UTS-500-Series/Compressor/kicad/connector.kicad_sch

## KiCad design kicad/connector.kicad_sch (2026-10-02)

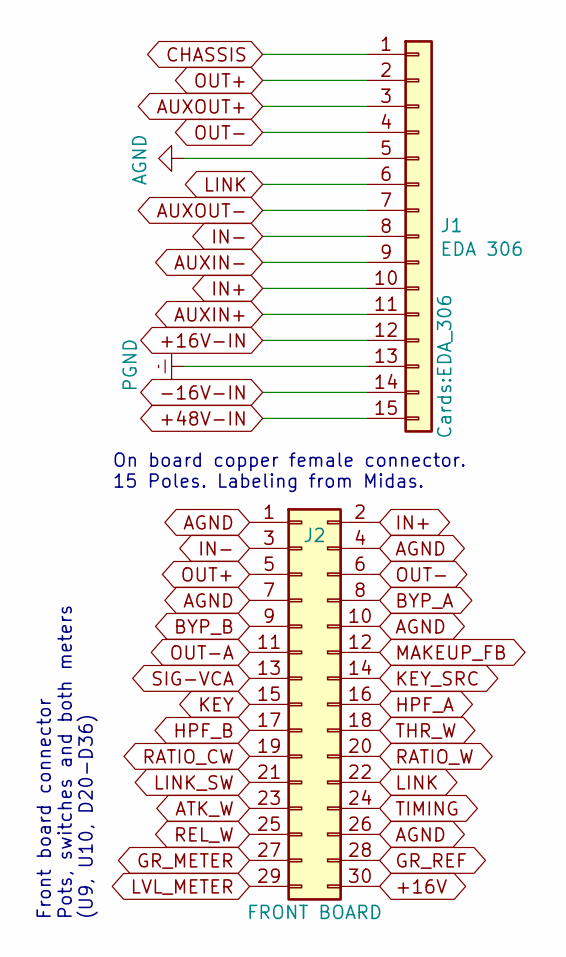
[picture p19: schematic connector.kicad_sch]

Parts:
J1: EDA 306; EDA_306
J2: FRONT BOARD; IDC-Header_2x15_P2.54mm_Vertical

Connections:
+16V: J2.30
+16V-IN: J1.12
+48V-IN: J1.15
-16V-IN: J1.14
AGND: J1.5, J2.1, J2.4, J2.7, J2.10, J2.26
ATK_W: J2.23
AUXIN+: J1.11
AUXIN-: J1.9
AUXOUT+: J1.3
AUXOUT-: J1.7
BYP_A: J2.8
BYP_B: J2.9
CHASSIS: J1.1
GR_METER: J2.27
GR_REF: J2.28
HPF_A: J2.16
HPF_B: J2.17
IN+: J1.10, J2.2
IN-: J1.8, J2.3
KEY: J2.15
KEY_SRC: J2.14
LINK: J1.6, J2.22
LINK_SW: J2.21
LVL_METER: J2.29
MAKEUP_FB: J2.12
OUT+: J1.2, J2.5
OUT-: J1.4, J2.6
OUT-A: J2.11
PGND: J1.13
RATIO_CW: J2.19
RATIO_W: J2.20
REL_W: J2.25
SIG-VCA: J2.13
THR_W: J2.18
TIMING: J2.24

Notes on the sheet:
Front board connector Pots, switches and both meters (U9, U10, D20-D36)
On board copper female connector. 15 Poles. Labeling from Midas.
