UTS-500-Series/Compressor/kicad/input.kicad_sch

## KiCad design kicad/input.kicad_sch (2026-10-02)

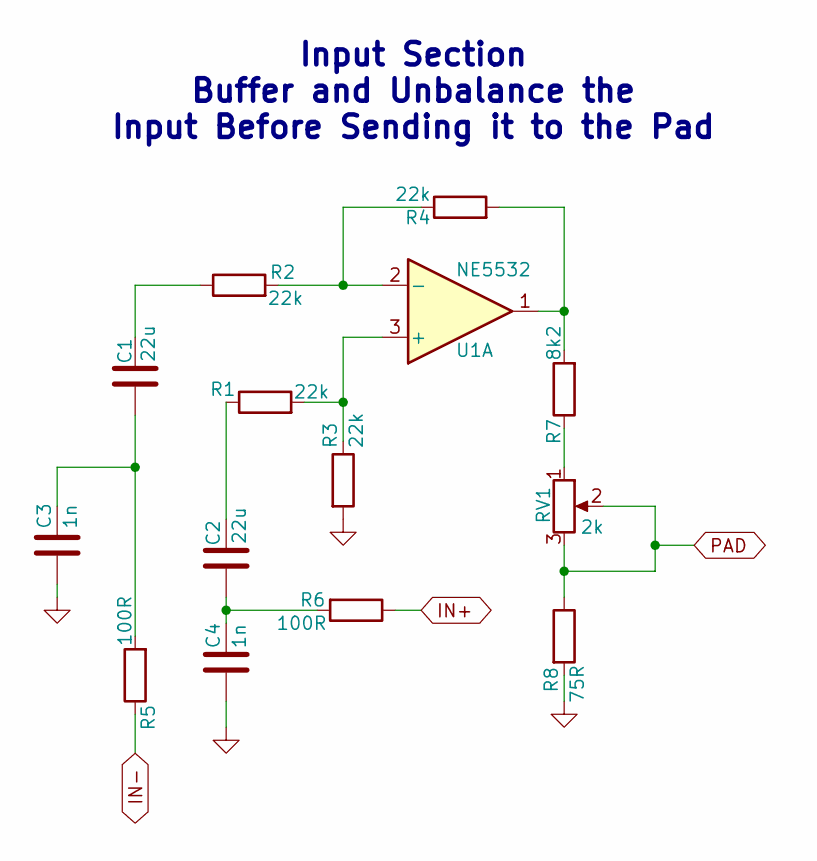
[picture p20: schematic input.kicad_sch]

Parts:
C1, C2: 22u; CP_Radial_D6.3mm_P2.50mm
C3, C4: 1n; C_Disc_D5.0mm_W2.5mm_P5.00mm
R1, R2, R3, R4: 22k; R_Axial_DIN0207_L6.3mm_D2.5mm_P10.16mm_Horizontal
R5, R6: 100R; R_Axial_DIN0207_L6.3mm_D2.5mm_P10.16mm_Horizontal
R7: 8k2; R_Axial_DIN0207_L6.3mm_D2.5mm_P10.16mm_Horizontal
R8: 75R; R_Axial_DIN0207_L6.3mm_D2.5mm_P10.16mm_Horizontal
RV1: 2k; Potentiometer_Bourns_3296W_Vertical
U1: NE5532; DIP-8_W7.62mm_Socket

Connections:
AGND: C3.2, C4.2, R3.2, R8.2
IN+: R6.1
IN-: R5.1
unnamed: C1.1, C3.1, R5.2
unnamed: C1.2, R2.1
unnamed: C2.1, C4.1, R6.2
unnamed: C2.2, R1.1
unnamed: R1.2, R3.1, U1.3 (+)
unnamed: R2.2, R4.1, U1.2 (-)
unnamed: R4.2, R7.2, U1.1
unnamed: R7.1, RV1.1
PAD: R8.1, RV1.2, RV1.3

Notes on the sheet:
Input Section Buffer and Unbalance the Input Before Sending it to the Pad
