UTS-500-Series/Compressor/kicad/meters.kicad_sch

## KiCad design kicad/meters.kicad_sch (2026-10-03)

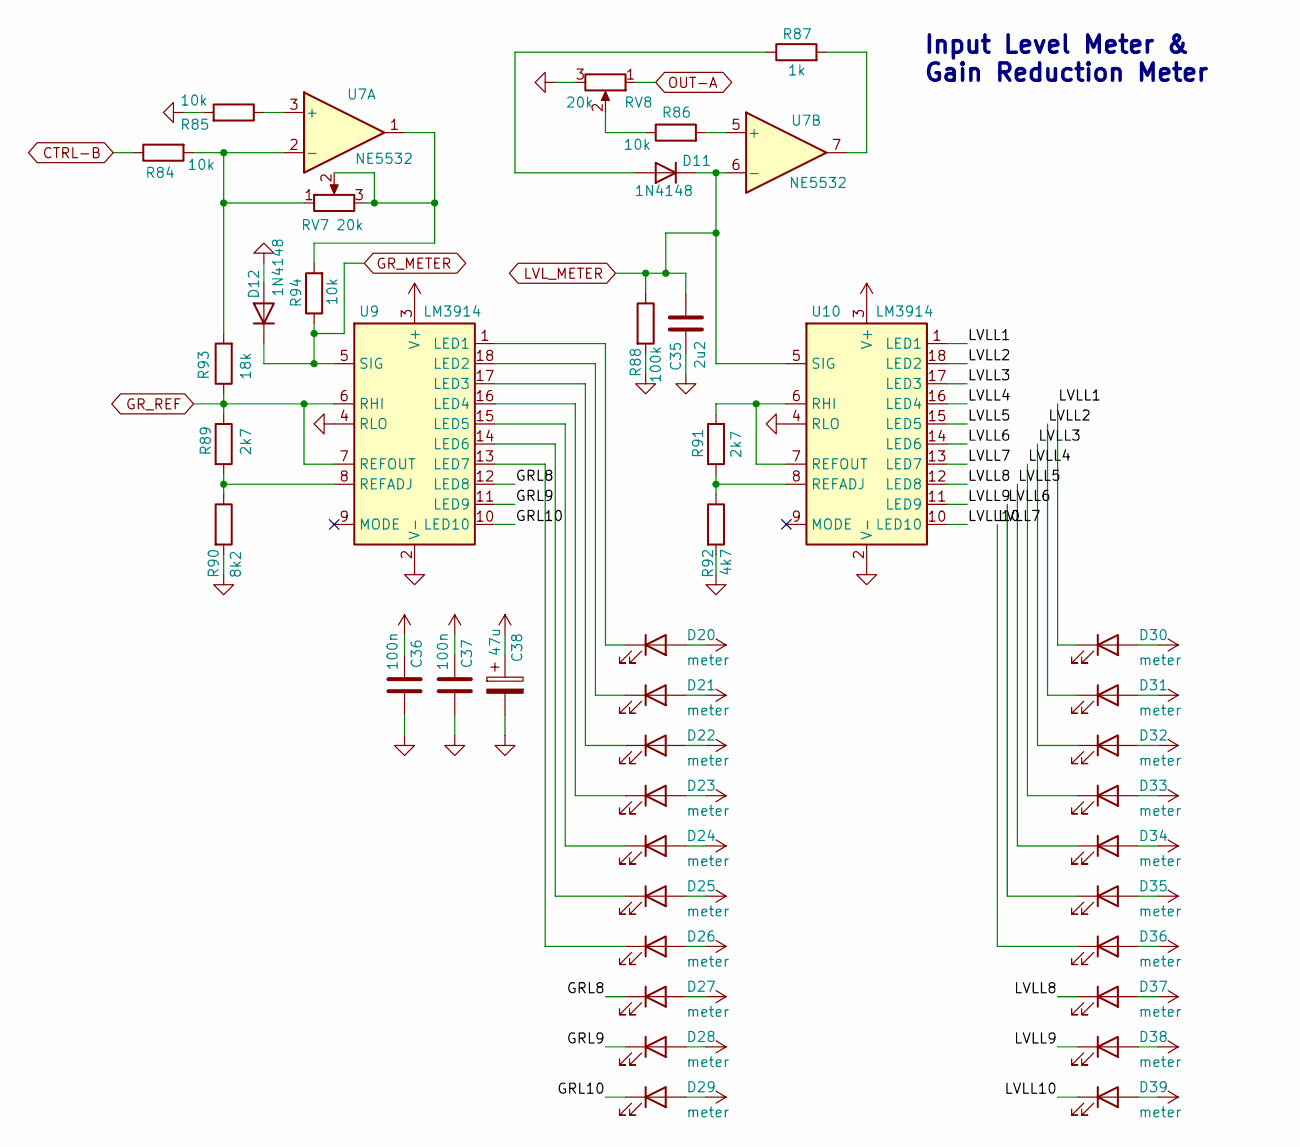
[picture p21: schematic meters.kicad_sch]

Parts:
C35: 2u2; C_Rect_L7.2mm_W7.2mm_P5.00mm_FKS2_FKP2_MKS2_MKP2
C36, C37: 100n; C_Disc_D5.0mm_W2.5mm_P5.00mm
C38: 47u; CP_Radial_D6.3mm_P2.50mm
D11, D12: 1N4148; D_DO-35_SOD27_P7.62mm_Horizontal
D20, D21, D22, D23, D24, D25, D26, D27, D28, D29, D30, D31, D32, D33, D34, D35, D36, D37, D38, D39: meter; LED_D2.0mm_W4.0mm_H2.8mm_FlatTop
R84, R85, R86, R94: 10k; R_Axial_DIN0207_L6.3mm_D2.5mm_P10.16mm_Horizontal
R87: 1k; R_Axial_DIN0207_L6.3mm_D2.5mm_P10.16mm_Horizontal
R88: 100k; R_Axial_DIN0207_L6.3mm_D2.5mm_P10.16mm_Horizontal
R89, R91: 2k7; R_Axial_DIN0207_L6.3mm_D2.5mm_P10.16mm_Horizontal
R90: 8k2; R_Axial_DIN0207_L6.3mm_D2.5mm_P7.62mm_Horizontal
R92: 4k7; R_Axial_DIN0207_L6.3mm_D2.5mm_P7.62mm_Horizontal
R93: 18k; R_Axial_DIN0207_L6.3mm_D2.5mm_P10.16mm_Horizontal
RV7, RV8: 20k; Potentiometer_Bourns_3296W_Vertical
U7: NE5532; DIP-8_W7.62mm_Socket
U9, U10: LM3914; DIP-18_W7.62mm

Connections:
+16V: C36.1, C37.1, C38.1, D20.2 (A), D21.2 (A), D22.2 (A), D23.2 (A), D24.2 (A), D25.2 (A), D26.2 (A), D27.2 (A), D28.2 (A), D29.2 (A), D30.2 (A), D31.2 (A), D32.2 (A), D33.2 (A), D34.2 (A), D35.2 (A), D36.2 (A), D37.2 (A), D38.2 (A), D39.2 (A), U9.3 (V+), U10.3 (V+)
AGND: C35.2, C36.2, C37.2, C38.2, D12.2 (A), R85.2, R88.2, R90.2, R92.2, RV8.3, U9.2 (V-), U9.4 (RLO), U10.2 (V-), U10.4 (RLO)
CTRL-B: R84.1
GRL8: D27.1 (K), U9.12 (LED8)
GRL9: D28.1 (K), U9.11 (LED9)
GRL10: D29.1 (K), U9.10 (LED10)
GR_METER: D12.1 (K), R94.1, U9.5 (SIG)
GR_REF: R89.1, R93.1, U9.6 (RHI), U9.7 (REFOUT)
LVLL1: D30.1 (K), U10.1 (LED1)
LVLL2: D31.1 (K), U10.18 (LED2)
LVLL3: D32.1 (K), U10.17 (LED3)
LVLL4: D33.1 (K), U10.16 (LED4)
LVLL5: D34.1 (K), U10.15 (LED5)
LVLL6: D35.1 (K), U10.14 (LED6)
LVLL7: D36.1 (K), U10.13 (LED7)
LVLL8: D37.1 (K), U10.12 (LED8)
LVLL9: D38.1 (K), U10.11 (LED9)
LVLL10: D39.1 (K), U10.10 (LED10)
LVL_METER: C35.1, D11.1 (K), R88.1, U7.6 (-), U10.5 (SIG)
unnamed: D11.2 (A), R87.1
unnamed: D20.1 (K), U9.1 (LED1)
unnamed: D21.1 (K), U9.18 (LED2)
unnamed: D22.1 (K), U9.17 (LED3)
unnamed: D23.1 (K), U9.16 (LED4)
unnamed: D24.1 (K), U9.15 (LED5)
unnamed: D25.1 (K), U9.14 (LED6)
unnamed: D26.1 (K), U9.13 (LED7)
unnamed: R84.2, R93.2, RV7.1, U7.2 (-)
unnamed: R85.1, U7.3 (+)
unnamed: R86.1, RV8.2
unnamed: R86.2, U7.5 (+)
unnamed: R87.2, U7.7
unnamed: R89.2, R90.1, U9.8 (REFADJ)
unnamed: R91.1, R92.1, U10.8 (REFADJ)
unnamed: R91.2, U10.6 (RHI), U10.7 (REFOUT)
unnamed: R94.2, RV7.2, RV7.3, U7.1
OUT-A: RV8.1

Notes on the sheet:
Input Level Meter & Gain Reduction Meter
