UTS-500-Series/Compressor/kicad/output.kicad_sch

## KiCad design kicad/output.kicad_sch (2026-10-02)

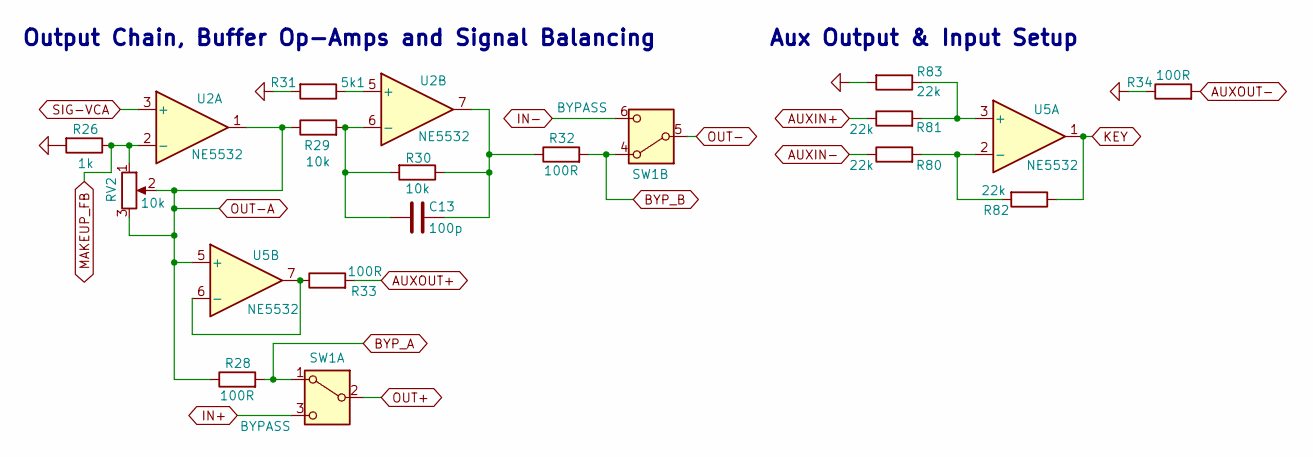
[picture p22: schematic output.kicad_sch]

Parts:
C13: 100p; C_Disc_D5.0mm_W2.5mm_P5.00mm
R26: 1k; R_Axial_DIN0207_L6.3mm_D2.5mm_P10.16mm_Horizontal
R28, R32, R33, R34: 100R; R_Axial_DIN0207_L6.3mm_D2.5mm_P10.16mm_Horizontal
R29, R30: 10k; R_Axial_DIN0207_L6.3mm_D2.5mm_P10.16mm_Horizontal
R31: 5k1; R_Axial_DIN0207_L6.3mm_D2.5mm_P10.16mm_Horizontal
R80, R81, R82, R83: 22k; R_Axial_DIN0207_L6.3mm_D2.5mm_P10.16mm_Horizontal
RV2: 10k; Potentiometer_Alps_RK09K_Single_Vertical
SW1: BYPASS; PinHeader_1x06_P2.54mm_Vertical
U2, U5: NE5532; DIP-8_W7.62mm_Socket

Connections:
AGND: R26.2, R31.2, R34.1, R83.2
AUXIN+: R81.1
AUXIN-: R80.1
AUXOUT+: R33.2
AUXOUT-: R34.2
BYP_A: R28.2, SW1.1 (A)
BYP_B: R32.2, SW1.4 (A)
IN+: SW1.3 (C)
IN-: SW1.6 (C)
KEY: R82.1, U5.1
MAKEUP_FB: R26.1, RV2.1, U2.2 (-)
unnamed: C13.1, R30.1, R32.1, U2.7
unnamed: C13.2, R29.2, R30.2, U2.6 (-)
unnamed: R31.1, U2.5 (+)
unnamed: R33.1, U5.6 (-), U5.7
unnamed: R80.2, R82.2, U5.2 (-)
unnamed: R81.2, R83.1, U5.3 (+)
OUT+: SW1.2 (B)
OUT-: SW1.5 (B)
OUT-A: R28.1, R29.1, RV2.2, RV2.3, U2.1, U5.5 (+)
SIG-VCA: U2.3 (+)

Notes on the sheet:
Output Chain, Buffer Op-Amps and Signal Balancing
Aux Output & Input Setup
