UTS-500-Series/Compressor/kicad/power.kicad_sch

## KiCad design kicad/power.kicad_sch (2026-10-02)

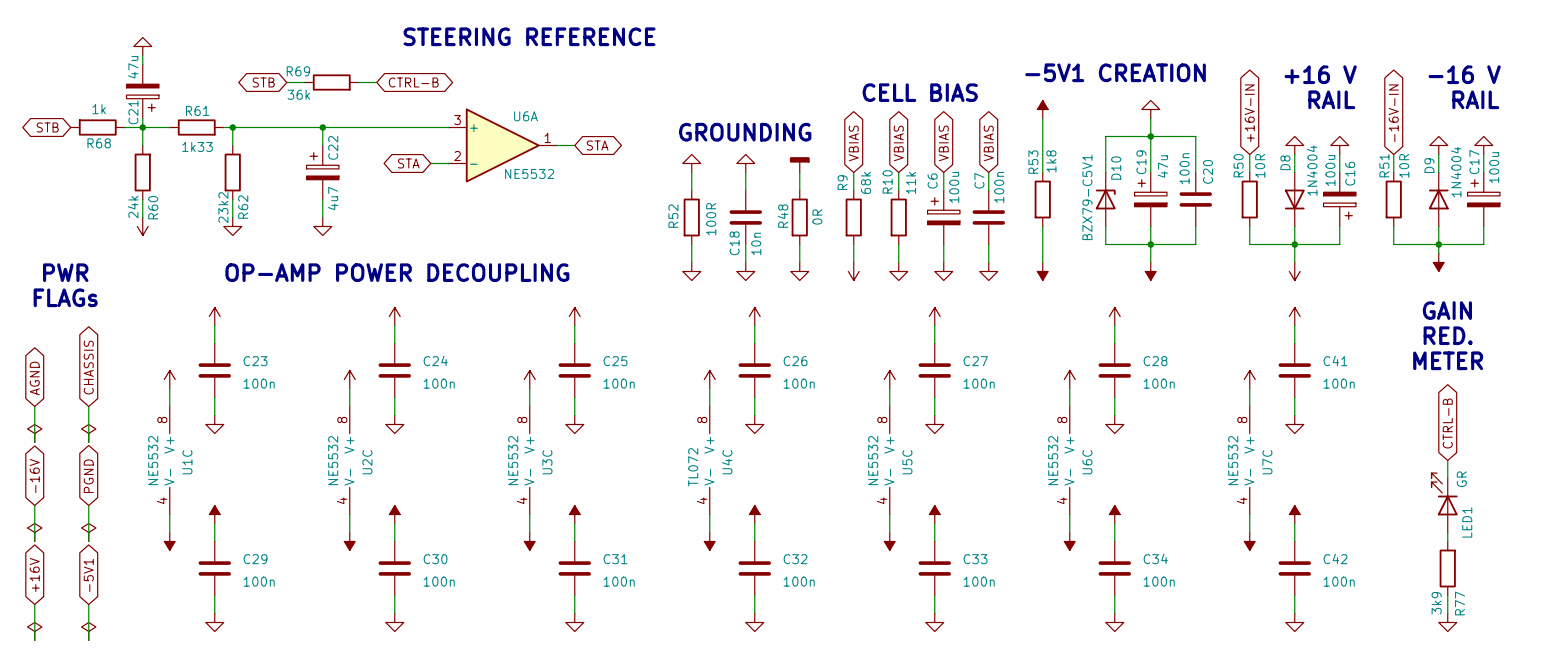
[picture p23: schematic power.kicad_sch]

Parts:
C6, C16, C17: 100u; CP_Radial_D6.3mm_P2.50mm
C7, C20, C23, C24, C25, C26, C27, C28, C29, C30, C31, C32, C33, C34, C41, C42: 100n; C_Disc_D5.0mm_W2.5mm_P5.00mm
C18: 10n; C_Disc_D5.0mm_W2.5mm_P5.00mm
C19, C21: 47u; CP_Radial_D6.3mm_P2.50mm
C22: 4u7; CP_Radial_D6.3mm_P2.50mm
D8, D9: 1N4004; D_DO-41_SOD81_P7.62mm_Horizontal
D10: BZX79-C5V1; D_DO-35_SOD27_P7.62mm_Horizontal
LED1: GR; LED_D3.0mm
R9: 68k; R_Axial_DIN0207_L6.3mm_D2.5mm_P10.16mm_Horizontal
R10: 11k; R_Axial_DIN0207_L6.3mm_D2.5mm_P10.16mm_Horizontal
R48: 0R; R_Axial_DIN0207_L6.3mm_D2.5mm_P10.16mm_Horizontal
R50, R51: 10R; R_Axial_DIN0207_L6.3mm_D2.5mm_P10.16mm_Horizontal
R52: 100R; R_Axial_DIN0207_L6.3mm_D2.5mm_P10.16mm_Horizontal
R53: 1k8; R_Axial_DIN0207_L6.3mm_D2.5mm_P10.16mm_Horizontal
R60: 24k; R_Axial_DIN0207_L6.3mm_D2.5mm_P10.16mm_Horizontal
R61: 1k33; R_Axial_DIN0207_L6.3mm_D2.5mm_P10.16mm_Horizontal
R62: 23k2; R_Axial_DIN0207_L6.3mm_D2.5mm_P10.16mm_Horizontal
R68: 1k; R_Axial_DIN0207_L6.3mm_D2.5mm_P10.16mm_Horizontal
R69: 36k; R_Axial_DIN0207_L6.3mm_D2.5mm_P10.16mm_Horizontal
R77: 3k9; R_Axial_DIN0207_L6.3mm_D2.5mm_P10.16mm_Horizontal
U1, U2, U3, U5, U6, U7: NE5532; DIP-8_W7.62mm_Socket
U4: TL072; DIP-8_W7.62mm_Socket

Connections:
+16V: C16.1, C23.1, C24.1, C25.1, C26.1, C27.1, C28.1, C41.1, D8.1 (K), R9.2, R50.2, R60.1, U1.8 (V+), U2.8 (V+), U3.8 (V+), U4.8 (V+), U5.8 (V+), U6.8 (V+), U7.8 (V+)
+16V-IN: R50.1
-5V1: C19.2, C20.1, D10.2 (A), R53.2
-16V: C17.2, C29.1, C30.1, C31.1, C32.1, C33.1, C34.1, C42.1, D9.2 (A), R51.2, R53.1, U1.4 (V-), U2.4 (V-), U3.4 (V-), U4.4 (V-), U5.4 (V-), U6.4 (V-), U7.4 (V-)
-16V-IN: R51.1
AGND: C6.2, C7.2, C16.2, C17.1, C18.2, C19.1, C20.2, C21.2, C22.2, C23.2, C24.2, C25.2, C26.2, C27.2, C28.2, C29.2, C30.2, C31.2, C32.2, C33.2, C34.2, C41.2, C42.2, D8.2 (A), D9.1 (K), D10.1 (K), R10.2, R48.2, R52.2, R62.2, R77.1
CHASSIS: C18.1, R52.1
CTRL-B: LED1.1 (K), R69.2
unnamed: C21.1, R60.2, R61.1, R68.1
unnamed: C22.1, R61.2, R62.1, U6.3 (+)
unnamed: LED1.2 (A), R77.2
PGND: R48.1
STA: U6.1, U6.2 (-)
STB: R68.2, R69.1
VBIAS: C6.1, C7.1, R9.1, R10.1

Notes on the sheet:
STEERING REFERENCE
+16 V RAIL
GROUNDING
-5V1 CREATION
CELL BIAS
OP-AMP POWER DECOUPLING
PWR FLAGs
-16 V RAIL
GAIN RED. METER
