UTS-500-Series/Compressor/kicad/sidechain.kicad_sch

## KiCad design kicad/sidechain.kicad_sch (2026-10-03)

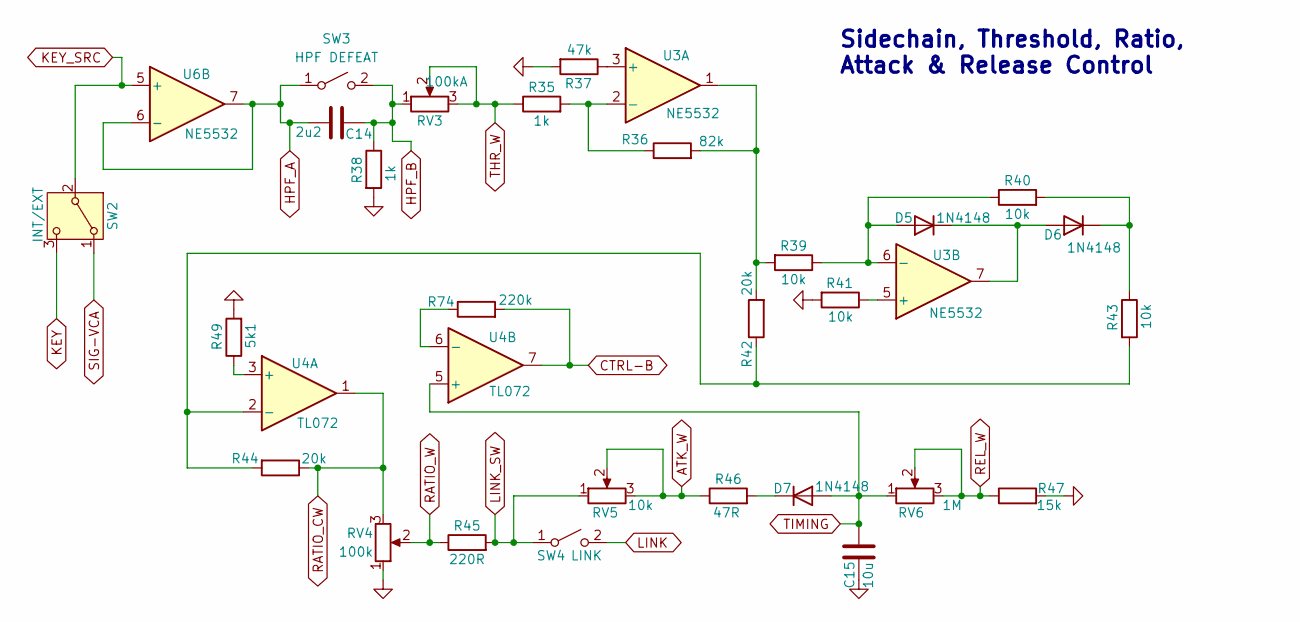
[picture p24: schematic sidechain.kicad_sch]

Parts:
C14: 2u2; C_Rect_L7.2mm_W7.2mm_P5.00mm_FKS2_FKP2_MKS2_MKP2
C15: 10u; C_Rect_L16.5mm_W11.8mm_P15.00mm_MKT
D5, D6, D7: 1N4148; D_DO-35_SOD27_P7.62mm_Horizontal
R35, R38: 1k; R_Axial_DIN0207_L6.3mm_D2.5mm_P10.16mm_Horizontal
R36: 82k; R_Axial_DIN0207_L6.3mm_D2.5mm_P10.16mm_Horizontal
R37: 47k; R_Axial_DIN0207_L6.3mm_D2.5mm_P10.16mm_Horizontal
R39, R40, R41, R43: 10k; R_Axial_DIN0207_L6.3mm_D2.5mm_P10.16mm_Horizontal
R42, R44: 20k; R_Axial_DIN0207_L6.3mm_D2.5mm_P10.16mm_Horizontal
R45: 220R; R_Axial_DIN0207_L6.3mm_D2.5mm_P10.16mm_Horizontal
R46: 47R; R_Axial_DIN0207_L6.3mm_D2.5mm_P10.16mm_Horizontal
R47: 15k; R_Axial_DIN0207_L6.3mm_D2.5mm_P10.16mm_Horizontal
R49: 5k1; R_Axial_DIN0207_L6.3mm_D2.5mm_P10.16mm_Horizontal
R74: 220k; R_Axial_DIN0207_L6.3mm_D2.5mm_P10.16mm_Horizontal
RV3: 100kA; Potentiometer_Alps_RK09K_Single_Vertical
RV4: 100k; Potentiometer_Alps_RK09K_Single_Vertical
RV5: 10k; Potentiometer_Alps_RK09K_Single_Vertical
RV6: 1M; Potentiometer_Alps_RK09K_Single_Vertical
SW2: INT/EXT; PinHeader_1x03_P2.54mm_Vertical
SW3: HPF DEFEAT; PinHeader_1x02_P2.54mm_Vertical
SW4: LINK; PinHeader_1x02_P2.54mm_Vertical
U3, U6: NE5532; DIP-8_W7.62mm_Socket
U4: TL072; DIP-8_W7.62mm_Socket

Connections:
AGND: C15.2, R37.2, R38.2, R41.2, R47.2, R49.2, RV4.1
ATK_W: R46.1, RV5.2, RV5.3
CTRL-B: R74.2, U4.7
HPF_A: C14.1, SW3.1 (A), U6.6 (-), U6.7
HPF_B: C14.2, R38.1, RV3.1, SW3.2 (B)
KEY: SW2.3 (C)
KEY_SRC: SW2.2 (B), U6.5 (+)
LINK: SW4.2 (B)
LINK_SW: R45.2, RV5.1, SW4.1 (A)
unnamed: D5.1 (K), D6.2 (A), U3.7
unnamed: D5.2 (A), R39.1, R40.1, U3.6 (-)
unnamed: D6.1 (K), R40.2, R43.1
unnamed: D7.1 (K), R46.2
unnamed: R35.2, R36.1, U3.2 (-)
unnamed: R36.2, R39.2, R42.2, U3.1
unnamed: R37.1, U3.3 (+)
unnamed: R41.1, U3.5 (+)
unnamed: R42.1, R43.2, R44.2, U4.2 (-)
unnamed: R49.1, U4.3 (+)
unnamed: R74.1, U4.6 (-)
RATIO_CW: R44.1, RV4.3, U4.1
RATIO_W: R45.1, RV4.2
REL_W: R47.1, RV6.2, RV6.3
SIG-VCA: SW2.1 (A)
THR_W: R35.1, RV3.2, RV3.3
TIMING: C15.1, D7.2 (A), RV6.1, U4.5 (+)

Notes on the sheet:
Sidechain, Threshold, Ratio, Attack & Release Control
