UTS-500-Series/Compressor/kicad/vca.kicad_sch

## KiCad design kicad/vca.kicad_sch (2026-10-02)

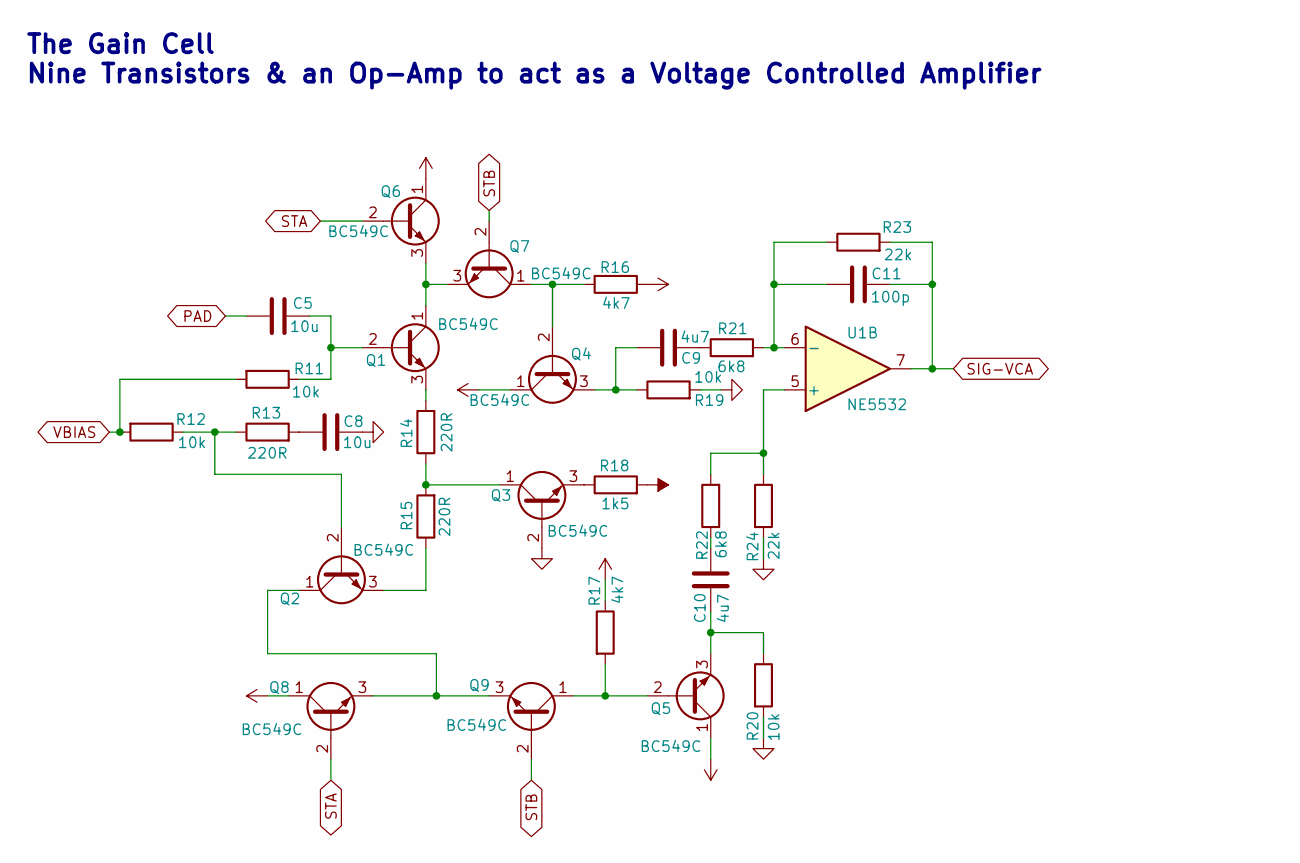
[picture p25: schematic vca.kicad_sch]

Parts:
C5, C8: 10u; C_Rect_L16.5mm_W11.8mm_P15.00mm_MKT
C9, C10: 4u7; C_Rect_L16.5mm_W7.3mm_P15.00mm_MKT
C11: 100p; C_Disc_D5.0mm_W2.5mm_P5.00mm
Q1, Q2, Q3, Q4, Q5, Q6, Q7, Q8, Q9: BC549C; TO-92_Inline
R11, R12, R19, R20: 10k; R_Axial_DIN0207_L6.3mm_D2.5mm_P10.16mm_Horizontal
R13, R14, R15: 220R; R_Axial_DIN0207_L6.3mm_D2.5mm_P10.16mm_Horizontal
R16, R17: 4k7; R_Axial_DIN0207_L6.3mm_D2.5mm_P10.16mm_Horizontal
R18: 1k5; R_Axial_DIN0207_L6.3mm_D2.5mm_P10.16mm_Horizontal
R21, R22: 6k8; R_Axial_DIN0207_L6.3mm_D2.5mm_P10.16mm_Horizontal
R23, R24: 22k; R_Axial_DIN0207_L6.3mm_D2.5mm_P10.16mm_Horizontal
U1: NE5532; DIP-8_W7.62mm_Socket

Connections:
+16V: Q4.1 (C), Q5.1 (C), Q6.1 (C), Q8.1 (C), R16.1, R17.1
-5V1: R18.2
AGND: C8.2, Q3.2 (B), R19.2, R20.2, R24.2
unnamed: C5.2, Q1.2 (B), R11.1
unnamed: C8.1, R13.2
unnamed: C9.1, Q4.3 (E), R19.1
unnamed: C9.2, R21.1
unnamed: C10.1, R22.1
unnamed: C10.2, Q5.3 (E), R20.1
unnamed: C11.1, R21.2, R23.1, U1.6 (-)
unnamed: Q1.1 (C), Q6.3 (E), Q7.3 (E)
unnamed: Q1.3 (E), R14.2
unnamed: Q2.1 (C), Q8.3 (E), Q9.3 (E)
unnamed: Q2.2 (B), R12.1, R13.1
unnamed: Q2.3 (E), R15.1
unnamed: Q3.1 (C), R14.1, R15.2
unnamed: Q3.3 (E), R18.1
unnamed: Q4.2 (B), Q7.1 (C), R16.2
unnamed: Q5.2 (B), Q9.1 (C), R17.2
unnamed: R22.2, R24.1, U1.5 (+)
PAD: C5.1
SIG-VCA: C11.2, R23.2, U1.7
STA: Q6.2 (B), Q8.2 (B)
STB: Q7.2 (B), Q9.2 (B)
VBIAS: R11.2, R12.2

Notes on the sheet:
The Gain Cell Nine Transistors & an Op-Amp to act as a Voltage Controlled Amplifier
